Tonikiller10000/EMG_WristSensor/BioSignalsDetectionDocuments/ECG_OUTPUT.webp

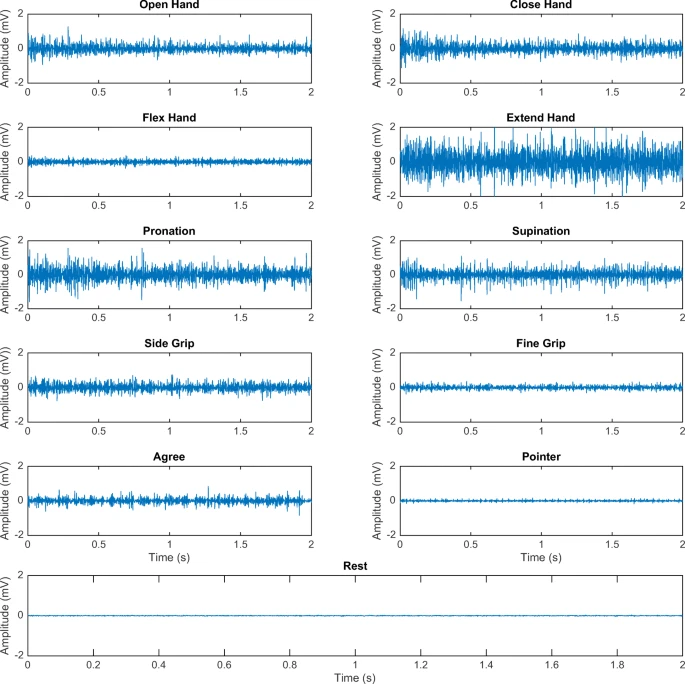
BioSignalsDetectionDocuments/ECG_OUTPUT.webp
