Tonikiller10000/EMG_WristSensor/BioSignalsDetectionDocuments/EMG (1).png

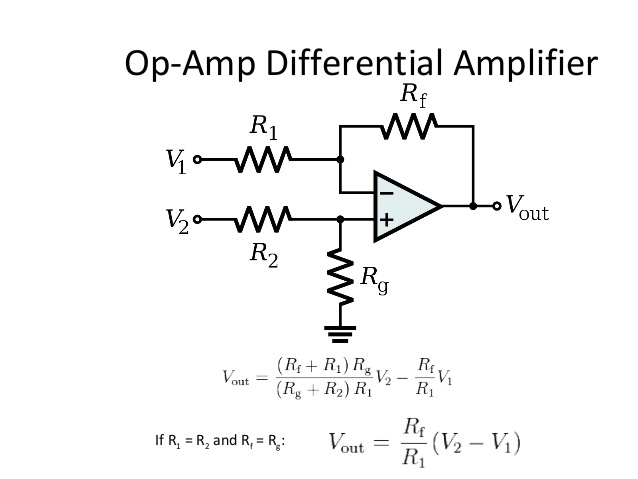
BioSignalsDetectionDocuments/EMG (1).png
