Tonikiller10000/EMG_WristSensor/BioSignalsDetectionDocuments/EMG (2).jpg

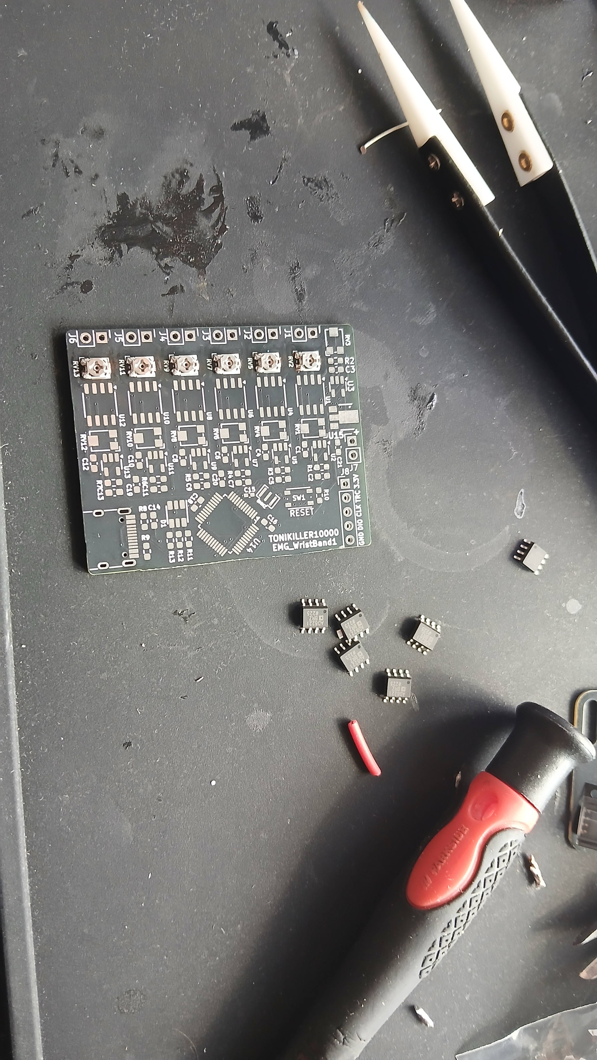
BioSignalsDetectionDocuments/EMG (2).jpg
