Tonikiller10000/EMG_WristSensor/BioSignalsDetectionDocuments/EMGGGGG (1).jpg

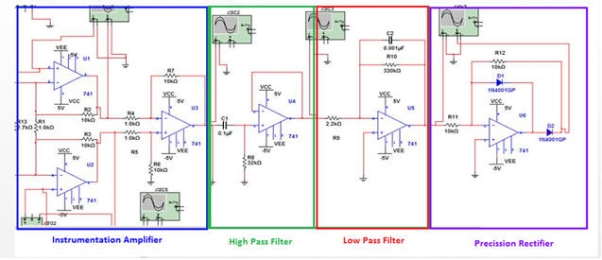
BioSignalsDetectionDocuments/EMGGGGG (1).jpg
