Tonikiller10000/EMG_WristSensor/BioSignalsDetectionDocuments/EMGGGGG (2).png

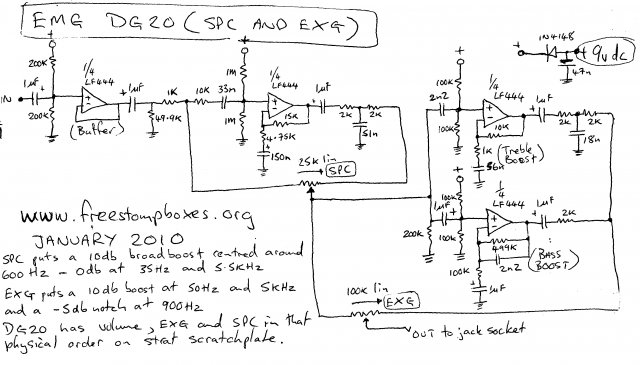
BioSignalsDetectionDocuments/EMGGGGG (2).png
