Tonikiller10000/EMG_WristSensor/BioSignalsDetectionDocuments/Screenshot 2024-10-06 195258.png

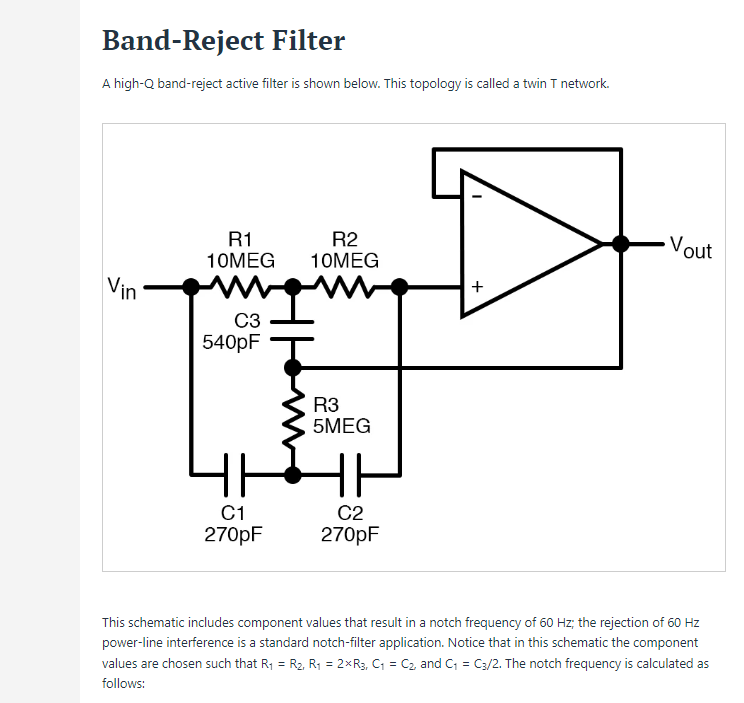
BioSignalsDetectionDocuments/Screenshot 2024-10-06 195258.png
