Tonikiller10000/EMG_WristSensor/BioSignalsDetectionDocuments/Screenshot 2024-10-07 214733.png

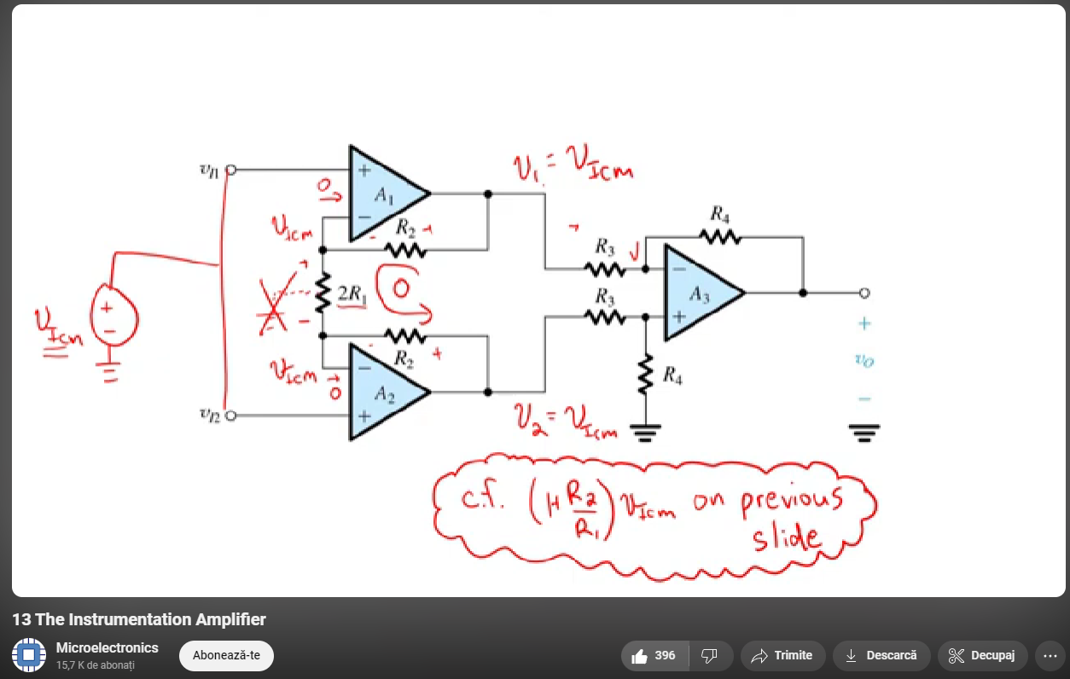
BioSignalsDetectionDocuments/Screenshot 2024-10-07 214733.png
