Tonikiller10000/EMG_WristSensor/BioSignalsDetectionDocuments/Screenshot 2024-10-08 005206.png

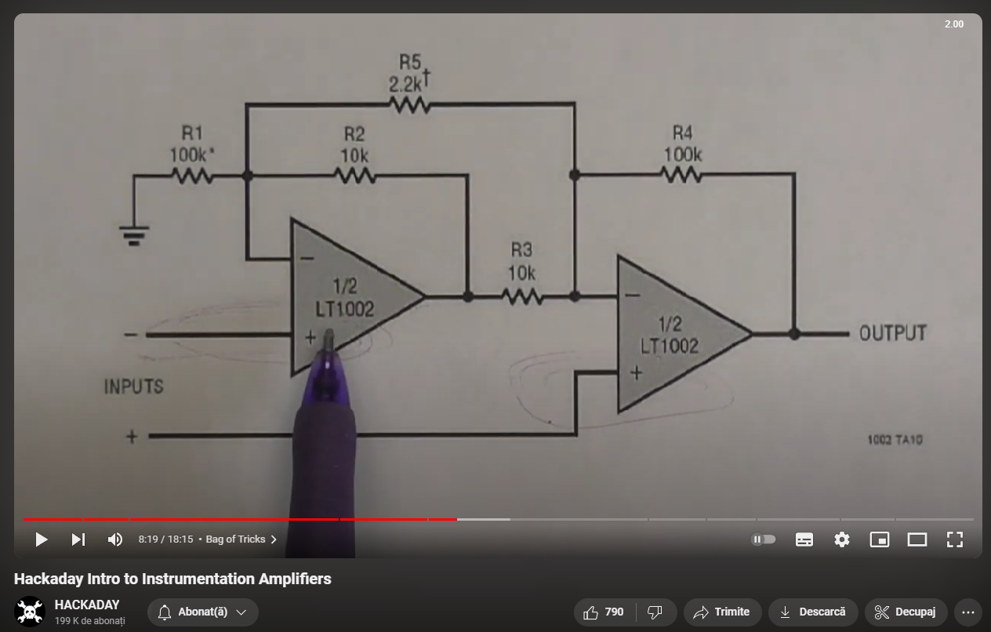
BioSignalsDetectionDocuments/Screenshot 2024-10-08 005206.png
