Tonikiller10000/EMG_WristSensor/BioSignalsDetectionDocuments/Screenshot 2024-10-08 192547.png

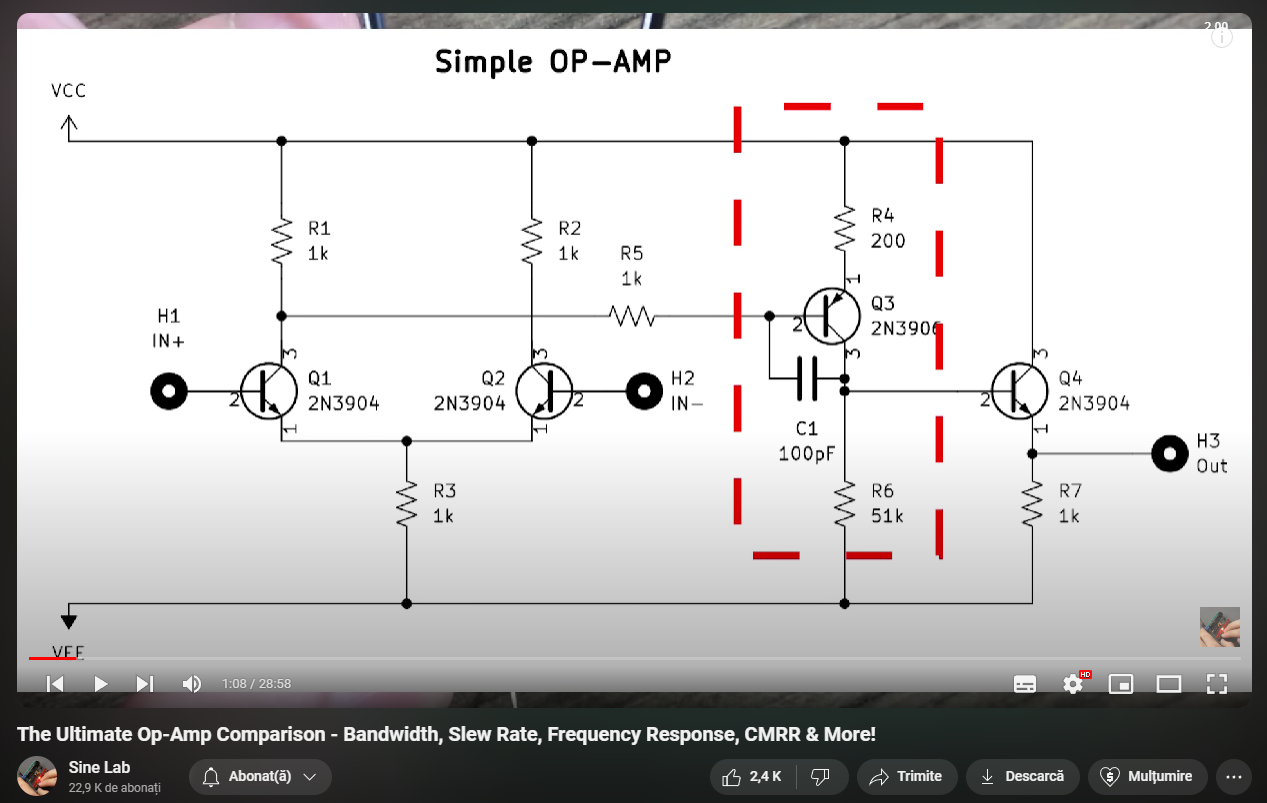
BioSignalsDetectionDocuments/Screenshot 2024-10-08 192547.png
