Tonikiller10000/EMG_WristSensor/BioSignalsDetectionDocuments/Screenshot 2024-10-14 163716.png

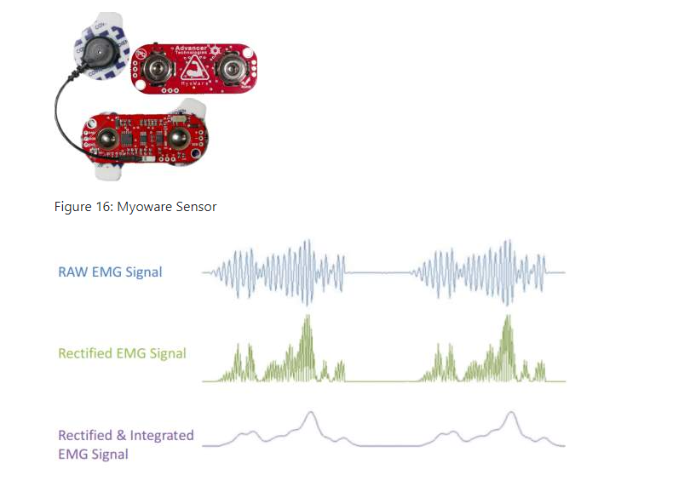
BioSignalsDetectionDocuments/Screenshot 2024-10-14 163716.png
